cdbrauer/EarthPod/Datalogging-Python/sample-logs/7-5-20/Anemometer vs. Thermal Airflow Sensor.png

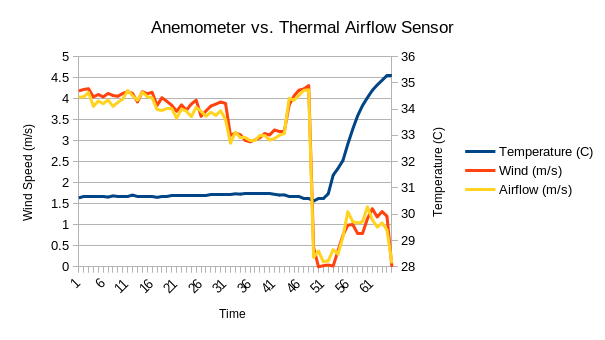
Datalogging-Python/sample-logs/7-5-20/Anemometer vs. Thermal Airflow Sensor.png
