cdbrauer/EarthPod/Datalogging-Python/sample-logs/7-6-20/Light.png

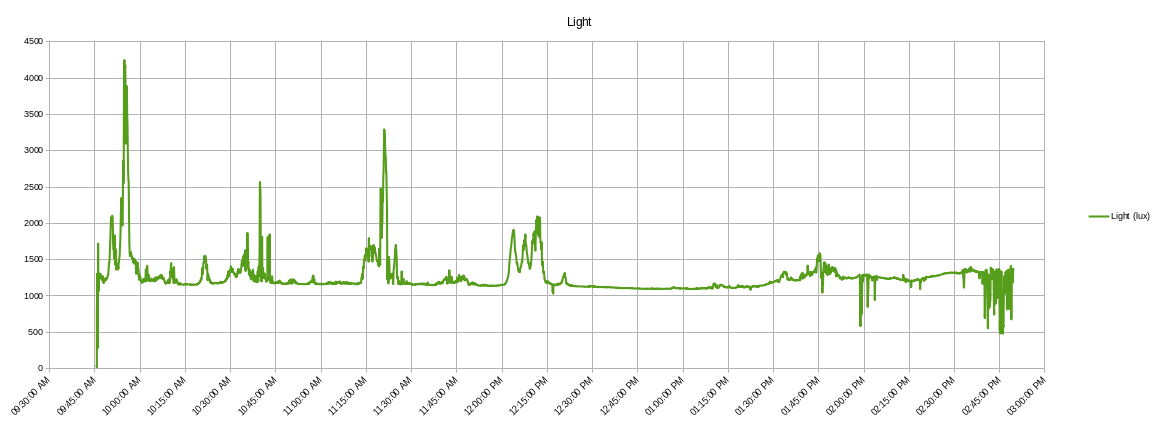
Datalogging-Python/sample-logs/7-6-20/Light.png
