cdbrauer/EarthPod/Datalogging-Python/sample-logs/7-6-20/Pressure.png

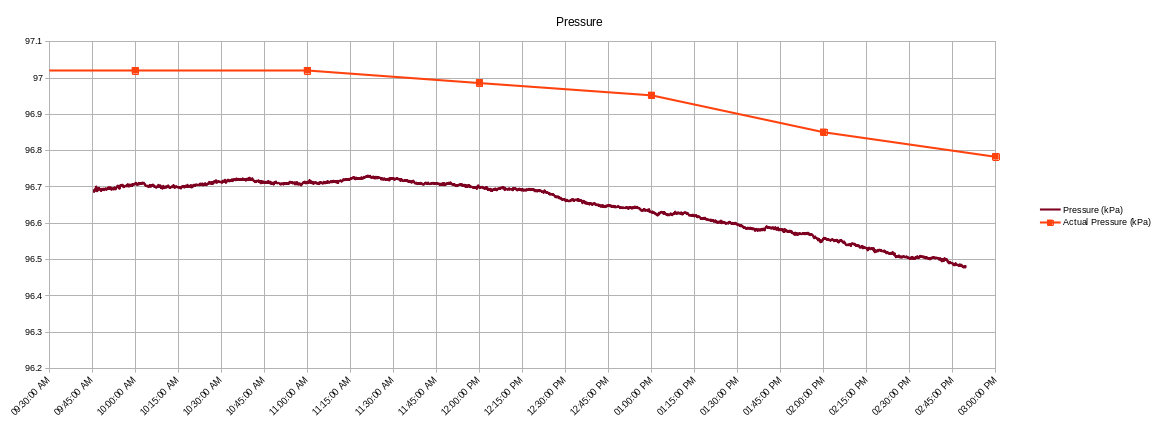
Datalogging-Python/sample-logs/7-6-20/Pressure.png
