cdbrauer/EarthPod/Datalogging-Python/sample-logs/7-6-20/Wind Sensor Comparison.png

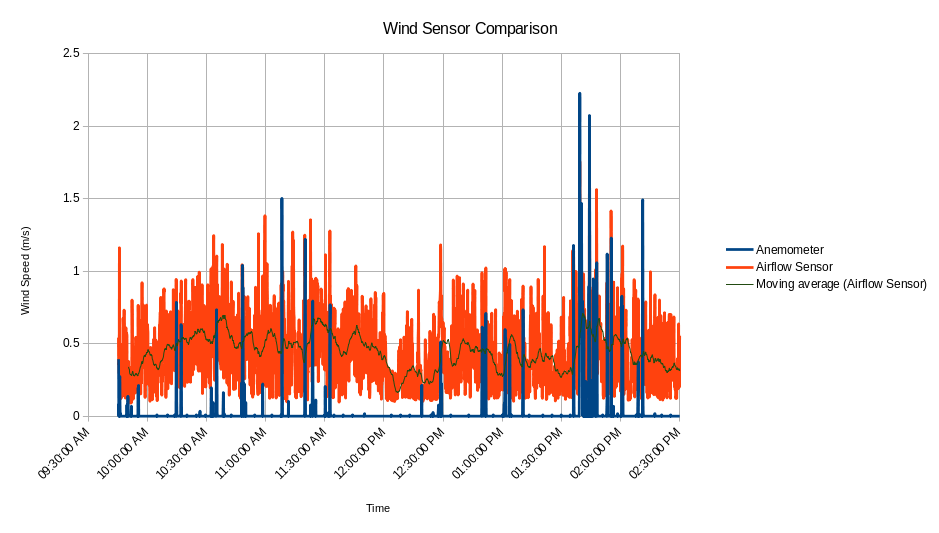
Datalogging-Python/sample-logs/7-6-20/Wind Sensor Comparison.png
