cdbrauer/EarthPod/Datalogging-Python/enviro_logging.py

"""
EarthPod Environment Logging

----

Copyright 2020 - Cole Brauer
"""

from coral.enviro.board import EnviroBoard
from coral.cloudiot.core import CloudIot
from luma.core.render import canvas
from PIL import ImageDraw
from time import sleep

import argparse
import itertools
import os
import time

DEFAULT_CONFIG_LOCATION = os.path.join(os.path.dirname(__file__), 'cloud_config.ini')

def update_display(display, msg):
    with canvas(display) as draw:
        draw.text((0, 0), msg, fill='white')

def check_nan(val):
    return float('nan') if val is None else val

if __name__ == '__main__':
    # Save program start time
    t0 = time.time()

    # Pull arguments from command line.
    parser = argparse.ArgumentParser(description='Enviro Kit Datalogging')
    parser.add_argument('--filename', help='File for storing sensor data logs', type=str, default=('Log_' + str(time.asctime(time.localtime(time.time()))).replace(' ', '_').replace(':', '-') + '.csv'))
    parser.add_argument('--time_step', help='Measurement logging interval (seconds)', type=int, default=5)
    parser.add_argument('--upload_step', help='Cloud upload interval (seconds)', type=int, default=300)
    parser.add_argument('--cloud_config', help='Cloud IoT config file', default=DEFAULT_CONFIG_LOCATION)
    parser.add_argument('--display', help='Enable printing data to terminal', type=int, default=False)
    args = parser.parse_args()

    # Create log file
    f = open(os.path.join(os.path.dirname(__file__), 'logs/') + args.filename, 'w+')
    f.write('EarthPod Sensor Log\n')
    f.write('Created: ' + str(time.asctime(time.localtime(time.time()))) + '\n\n')
    f.write('Measurement Time,Time Step (s),Temperature (C),Humidity (%),Light (lux),Pressure (kPa)\n')
    f.close()

    # Create instances of EnviroKit and Cloud IoT.
    enviro = EnviroBoard()
    with CloudIot(args.cloud_config) as cloud:
        # Indefinitely update display and upload to cloud.
        sensors = {}
        read_period = int(args.upload_step / args.time_step)

        for read_count in itertools.count():
            # Read sensors
            sensors['time'] = str(time.asctime(time.localtime(time.time())))
            sensors['time_step'] = round(time.time() - t0, 3)
            t0 = time.time()
            sensors['temperature'] = enviro.temperature
            sensors['humidity'] = enviro.humidity
            sensors['ambient_light'] = enviro.ambient_light
            sensors['pressure'] = enviro.pressure

            # Save latest data
            f = open(os.path.join(os.path.dirname(__file__), 'logs/') + args.filename, 'a+')
            f.write(str(sensors['time']) + ',')
            f.write(str(sensors['time_step']) + ',')
            f.write(str(sensors['temperature']) + ',')
            f.write(str(sensors['humidity']) + ',')
            f.write(str(sensors['ambient_light']) + ',')
            f.write(str(sensors['pressure']) + '\n')
            f.close()

            # Print data to terminal
            if args.display:
                print(str(sensors))

            # Display temperature and RH
            msg = 'Temp: %.2f C\n' % check_nan(sensors['temperature'])
            msg += 'RH: %.2f %%' % check_nan(sensors['humidity'])
            update_display(enviro.display, msg)
            sleep(args.time_step / 2)

            # After half of time_step, switch to light and pressure.
            msg = 'Light: %.2f lux\n' % check_nan(sensors['ambient_light'])
            msg += 'Pressure: %.2f kPa' % check_nan(sensors['pressure'])
            update_display(enviro.display, msg)
            sleep(args.time_step / 2)

            # If time has elapsed, attempt cloud upload.
            if read_count % read_period == 0 and cloud.enabled():
                print('Publishing')
                cloud.publish_message(sensors)
